dektronics/printalyzer-timer/enclosure/jigs/jig-power-board-2.stl

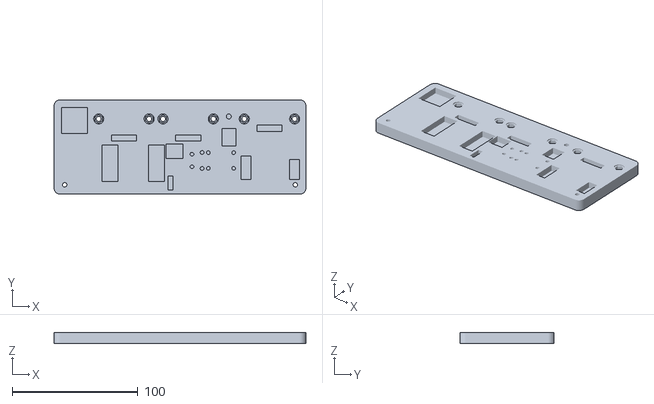
[picture p26: CAD file, 2024-06-14]
enclosure/jigs/jig-power-board-2.stl
200.0 x 75.0 x 9.00
