dektronics/printalyzer-timer/enclosure/meter-probe/meter-probe-bottom.3mf

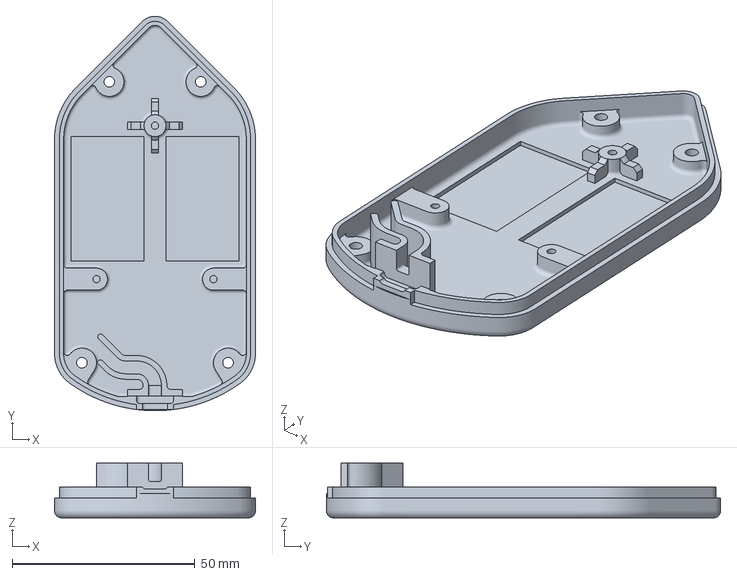
[picture p27: CAD file, 2026-03-26]
enclosure/meter-probe/meter-probe-bottom.3mf
55.0 x 107.9 x 15.0 mm
