dektronics/printalyzer-timer/enclosure/densistick/densistick-enclosure.step

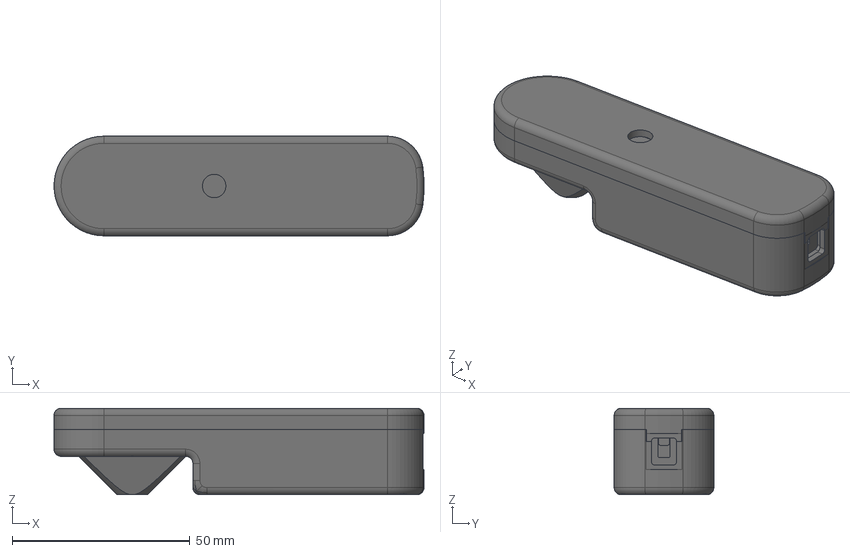
[picture p28: CAD file, 2026-03-26]
enclosure/densistick/densistick-enclosure.step
104.0 x 28.0 x 24.3 mm
Main Housing
Main Cover
Sensor Board Cover
Lower Filter Ring
Upper Filter Ring
