dektronics/printalyzer-timer/enclosure/meter-probe/meter-probe-top-rear.dxf

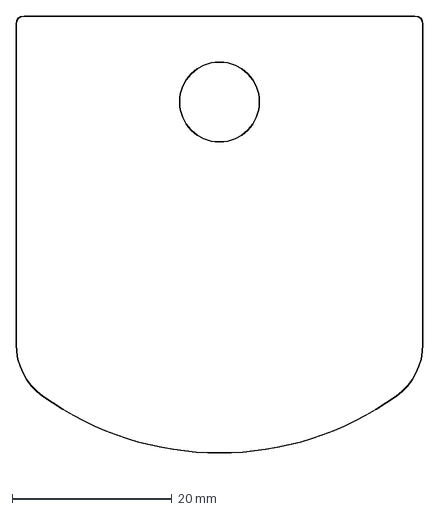
[picture p29: CAD file, 2024-02-04]
enclosure/meter-probe/meter-probe-top-rear.dxf
51.0 x 57.1 mm
