dektronics/printalyzer-timer/enclosure/base-unit/enclosure-base-flat.dxf

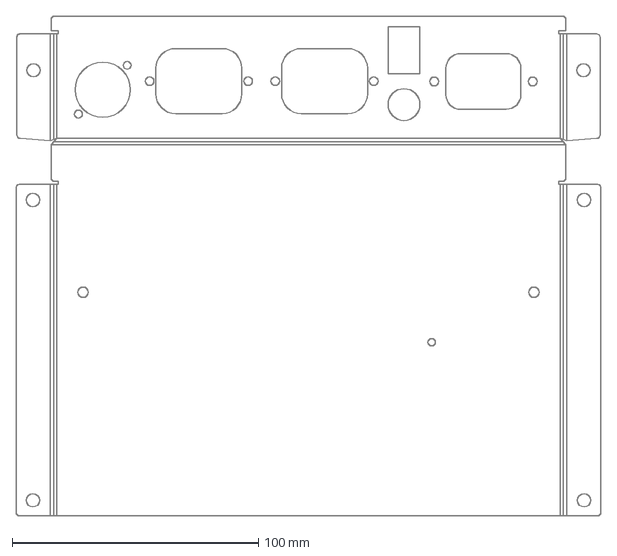
[picture p30: CAD file, 2026-03-26]
enclosure/base-unit/enclosure-base-flat.dxf
237.3 x 202.9 mm
