dektronics/printalyzer-timer/enclosure/densistick/densistick-cover.3mf

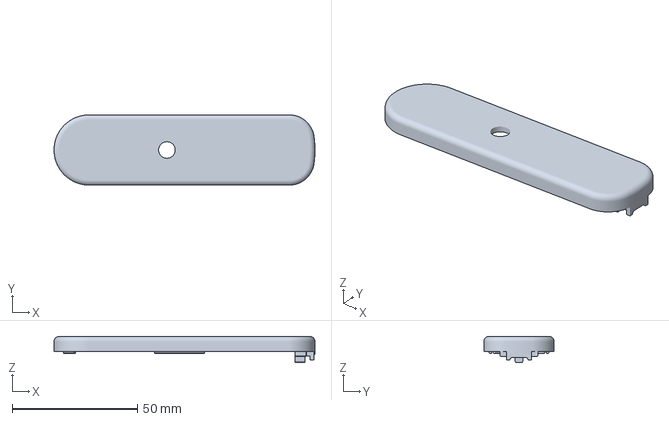
[picture p31: CAD file, 2026-03-26]
enclosure/densistick/densistick-cover.3mf
104.0 x 28.0 x 10.4 mm
