dektronics/printalyzer-timer/enclosure/meter-probe/meter-probe-top-front.dxf

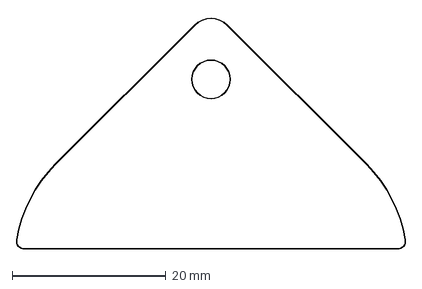
[picture p32: CAD file, 2024-02-04]
enclosure/meter-probe/meter-probe-top-front.dxf
50.6 x 30.3 mm
