dektronics/printalyzer-timer/enclosure/densistick/upper-filter-ring.dxf

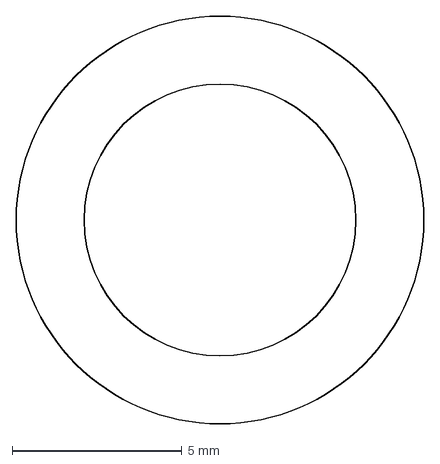
[picture p33: CAD file, 2024-08-25]
enclosure/densistick/upper-filter-ring.dxf
12.0 x 12.0 mm
