dektronics/printalyzer-timer/enclosure/densistick/densistick-overlay.dxf

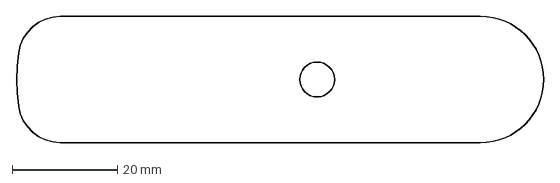
[picture p34: CAD file, 2024-08-25]
enclosure/densistick/densistick-overlay.dxf
100.1 x 24.0 mm
