dektronics/printalyzer-timer/enclosure/jigs/jig-power-board-1.stl

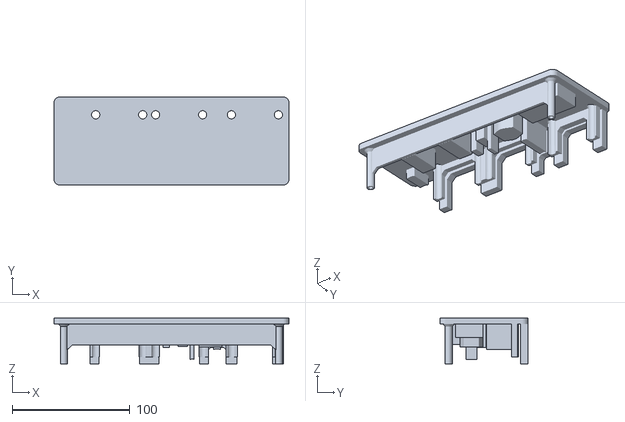
[picture p35: CAD file, 2024-06-14]
enclosure/jigs/jig-power-board-1.stl
200.0 x 75.0 x 39.0
