dektronics/printalyzer-timer/enclosure/meter-probe/meter-probe-top-rear-drawing.pdf

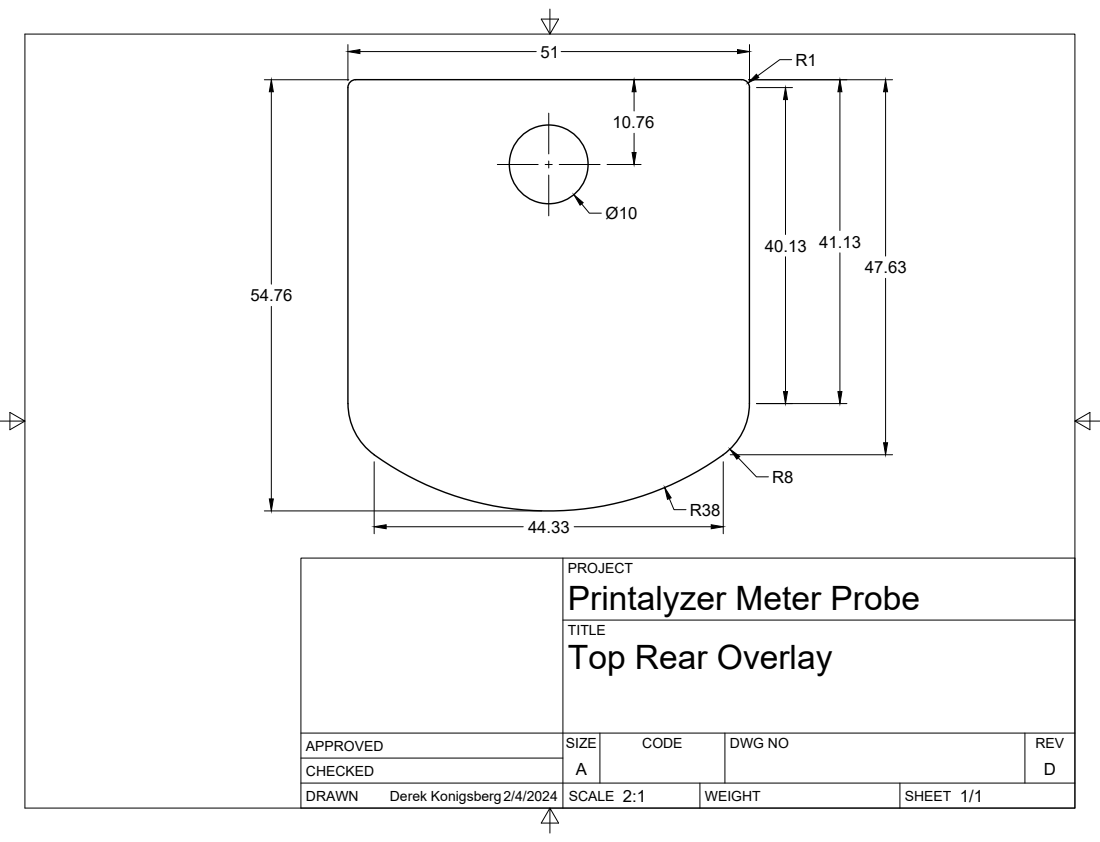
[picture p56: page 1]
SIZE; CODE; DWG NO; REV; Derek Konigsberg2/4/2024

PROJECT
Printalyzer Meter Probe
Top Rear Overlay
