dektronics/printalyzer-timer/enclosure/meter-probe/meter-probe-top-rear.pdf

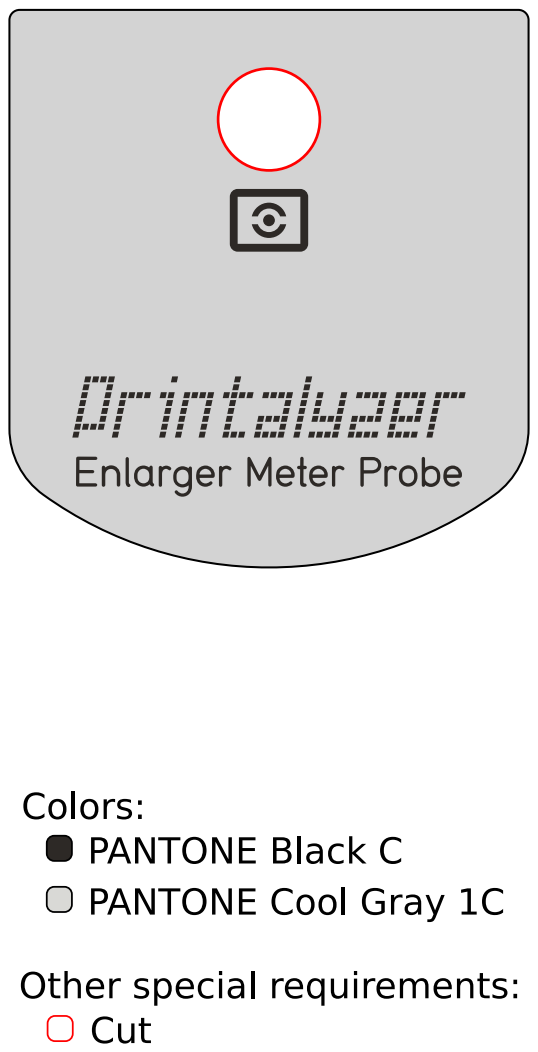
[picture p58: page 1]
