dektronics/printalyzer-timer/docs/cube/printalyzer-timer.ioc

Mcu.UserName=STM32F446RETx
PA0-WKUP.GPIO_Label=BUZZ_EN1 [Piezo]
PA0-WKUP.Signal=GPIO_Output
PA1.GPIO_Label=BUZZ_EN2 [Piezo]
PA1.Signal=GPIO_Output
PA10.Signal=USART1_RX
PA11.GPIO_Label=DMX512_RX_EN
PA11.Signal=GPIO_Output
PA13.Signal=SYS_JTMS-SWDIO
PA14.Signal=SYS_JTCK-SWCLK
PA15.Signal=SYS_JTDI
PA2.GPIO_Label=BUZZ_DIN [Piezo]
PA2.Signal=S_TIM9_CH1
PA4.GPIO_Label=DISP_CS [Display]
PA4.Signal=GPIO_Output
PA5.GPIO_Label=DISP_SCK [Display]
PA5.Signal=SPI1_SCK
PA6.GPIO_Label=DISP_DC [Display]
PA6.Signal=GPIO_Output
PA7.GPIO_Label=DISP_MOSI [Display]
PA7.Signal=SPI1_MOSI
PA8.GPIO_Label=ENC_CH1
PA8.Signal=S_TIM1_CH1
PA9.GPIO_Label=ENC_CH2
PA9.Signal=S_TIM1_CH2
PB0.GPIO_Label=LED_OE [LED Driver]
PB0.Signal=S_TIM3_CH3
PB10.Signal=I2C2_SCL
PB12.GPIO_Label=USB_HUB_RESET
PB12.Signal=GPIO_Output
PB13.GPIO_Label=USB_DRIVE_VBUS
PB13.Signal=GPIO_Output
PB14.Signal=USB_OTG_HS_DM
PB15.Signal=USB_OTG_HS_DP
PB3.Signal=SYS_JTDO-SWO
PB5.GPIO_Label=KEY_INT [Keypad]
PB5.Signal=GPXTI5
PB6.Signal=USART1_TX
PB7.Signal=I2C1_SDA
PB8.Signal=I2C1_SCL
PC1.GPIO_Label=LED_SDI [LED Driver]
PC1.Signal=SPI3_MOSI
PC10.GPIO_Label=LED_CLK [LED Driver]
PC10.Signal=SPI3_SCK
PC11.GPIO_Label=RELAY_SFLT [Safelight]
PC11.Signal=GPIO_Output
PC12.Signal=I2C2_SDA
PC2.GPIO_Label=LED_LE [LED Driver]
PC2.Signal=GPIO_Output
PC4.GPIO_Label=DISP_RESET [Display]
PC4.Signal=GPIO_Output
PC6.GPIO_Label=DMX512_TX
PC6.Signal=USART6_TX
PC7.GPIO_Label=DMX512_RX
PC7.Signal=USART6_RX
PC8.GPIO_Label=DMX512_TX_EN
PC8.Signal=GPIO_Output
PC9.GPIO_Label=USB_HUB_CLK
PC9.Signal=RCC_MCO_2
PD2.GPIO_Label=RELAY_ENLG [Enlarger]
PD2.Signal=GPIO_Output
PH0-OSC_IN.Signal=RCC_OSC_IN
PH1-OSC_OUT.Signal=RCC_OSC_OUT
