dektronics/printalyzer-timer/software/firmware/src/display/display_assets.c

#include "display_assets.h"

#include <string.h>

#define printalyzer_width 256
#define printalyzer_height 64
static const unsigned char printalyzer_bits[] = {
    0x00, 0x00, 0x00, 0x00, 0x00, 0x00, 0x00, 0x00, 0x00, 0x00, 0x00, 0x00,
    0x00, 0x00, 0x00, 0x00, 0x00, 0x00, 0x00, 0x00, 0x00, 0x00, 0x00, 0x00,
    0x00, 0x00, 0x00, 0x00, 0x00, 0x00, 0x00, 0x00, 0x00, 0x00, 0x00, 0x00,
    0x00, 0x00, 0x00, 0x00, 0x00, 0x00, 0x00, 0x00, 0x00, 0x00, 0x00, 0x00,
    0x00, 0x00, 0x00, 0x00, 0x00, 0x00, 0x00, 0x00, 0x00, 0x00, 0x00, 0x00,
    0x00, 0x00, 0x00, 0x00, 0x00, 0x00, 0x00, 0x00, 0x00, 0x00, 0x00, 0x00,
    0x00, 0x00, 0x00, 0x00, 0x00, 0x00, 0x00, 0x00, 0x00, 0x00, 0x00, 0x00,
    0x00, 0x00, 0x00, 0x00, 0x00, 0x00, 0x00, 0x00, 0x00, 0x00, 0x00, 0x00,
    0x00, 0x00, 0x00, 0x00, 0x00, 0x00, 0x00, 0x00, 0x00, 0x00, 0x00, 0x00,
    0x00, 0x00, 0x00, 0x00, 0x00, 0x00, 0x00, 0x00, 0x00, 0x00, 0x00, 0x00,
    0x00, 0x00, 0x00, 0x00, 0x00, 0x00, 0x00, 0x00, 0x00, 0x00, 0x00, 0x00,
    0x00, 0x00, 0x00, 0x00, 0x00, 0x00, 0x00, 0x00, 0x00, 0x00, 0x00, 0x00,
    0x00, 0x00, 0x00, 0x00, 0x00, 0x00, 0x00, 0x00, 0x00, 0x00, 0x00, 0x00,
    0x00, 0x00, 0x00, 0x00, 0x00, 0x00, 0x00, 0x00, 0x00, 0x00, 0x00, 0x00,
    0x00, 0x00, 0x00, 0x00, 0x00, 0x00, 0x00, 0x00, 0x00, 0x00, 0x00, 0x00,
    0x00, 0x00, 0x00, 0x00, 0x00, 0x00, 0x00, 0x00, 0x00, 0x00, 0x00, 0x00,
    0x00, 0x00, 0x00, 0x00, 0x00, 0x00, 0x00, 0x00, 0x00, 0x00, 0x00, 0x00,
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
    0x07, 0x63, 0x0c, 0x0e, 0x07, 0x07, 0x0e, 0x0e, 0x07, 0x0e, 0x07, 0x0e,
    0x07, 0xfc, 0x03, 0x0e, 0x07, 0xf0, 0x00, 0x0e, 0x07, 0x00, 0x00, 0x0e,
    0x07, 0x00, 0x00, 0x0e, 0xff, 0xff, 0xff, 0x0f, 0xfe, 0xff, 0xff, 0x07,
    0xf8, 0xff, 0xff, 0x01 };

#define dens_ind_refl_width 22
#define dens_ind_refl_height 22
static unsigned char dens_ind_refl_bits[] = {
    0x00, 0x0c, 0x00, 0x00, 0x0c, 0x00, 0x80, 0x7f, 0x00, 0xe0, 0xff, 0x01,
    0xf0, 0xcc, 0x03, 0x38, 0x0c, 0x07, 0x18, 0x00, 0x06, 0x1c, 0x00, 0x0e,
    0x0c, 0x00, 0x0c, 0x0c, 0x0c, 0x0c, 0x3f, 0x1e, 0x3f, 0x3f, 0x1e, 0x3f,
    0x0c, 0x0c, 0x0c, 0x0c, 0x00, 0x0c, 0x1c, 0x00, 0x0e, 0x18, 0x00, 0x06,
    0x38, 0x0c, 0x07, 0xf0, 0xcc, 0x03, 0xe0, 0xff, 0x01, 0x80, 0x7f, 0x00,
    0x00, 0x0c, 0x00, 0x00, 0x0c, 0x00 };

#define dens_ind_tran_width 22
#define dens_ind_tran_height 22
static unsigned char dens_ind_tran_bits[] = {
    0x00, 0x00, 0x00, 0x00, 0x0c, 0x00, 0x80, 0x7f, 0x00, 0xe0, 0xff, 0x01,
    0xf0, 0xc0, 0x03, 0x38, 0x00, 0x07, 0x18, 0x0c, 0x06, 0x1c, 0x0c, 0x0e,
    0x0c, 0x0c, 0x0c, 0x0c, 0x1e, 0x0c, 0xce, 0xff, 0x1c, 0xce, 0xff, 0x1c,
    0x0c, 0x1e, 0x0c, 0x0c, 0x0c, 0x0c, 0x1c, 0x0c, 0x0e, 0x18, 0x0c, 0x06,
    0x38, 0x00, 0x07, 0xf0, 0xc0, 0x03, 0xe0, 0xff, 0x01, 0x80, 0x7f, 0x00,
    0x00, 0x0c, 0x00, 0x00, 0x00, 0x00 };

#define ASSET_ENTRY(x) { x##_bits, x##_width, x##_height }

static const asset_info_t asset_list[] = {
    ASSET_ENTRY(printalyzer),
    ASSET_ENTRY(timer_icon_48),
    ASSET_ENTRY(timer_icon_32),
    ASSET_ENTRY(timer_icon_24),
    ASSET_ENTRY(timer_off_icon_24),
    ASSET_ENTRY(timer_off_icon_18),
    ASSET_ENTRY(exposure_adj_icon_48),
    ASSET_ENTRY(timer_adj_icon_48),
    ASSET_ENTRY(pev_adj_icon_48),
    ASSET_ENTRY(photo_icon_24),
    ASSET_ENTRY(adjust_icon_24),
    ASSET_ENTRY(adjust_count_1_18),
    ASSET_ENTRY(adjust_count_2_18),
    ASSET_ENTRY(adjust_count_3_18),
    ASSET_ENTRY(adjust_count_4_18),
    ASSET_ENTRY(adjust_count_5_18),
    ASSET_ENTRY(adjust_count_6_18),
    ASSET_ENTRY(adjust_count_7_18),
    ASSET_ENTRY(adjust_count_8_18),
    ASSET_ENTRY(adjust_count_9_18),
    ASSET_ENTRY(adjust_count_9p_18),
    ASSET_ENTRY(arrow_up_18),
    ASSET_ENTRY(arrow_down_18),
    ASSET_ENTRY(adjust_count_1_32),
    ASSET_ENTRY(adjust_count_2_32),
    ASSET_ENTRY(adjust_count_3_32),
    ASSET_ENTRY(adjust_count_4_32),
    ASSET_ENTRY(adjust_count_5_32),
    ASSET_ENTRY(adjust_count_6_32),
    ASSET_ENTRY(adjust_count_7_32),
    ASSET_ENTRY(adjust_count_8_32),
    ASSET_ENTRY(adjust_count_9_32),
    ASSET_ENTRY(adjust_count_9p_32),
    ASSET_ENTRY(paper_index_1_18),
    ASSET_ENTRY(paper_index_2_18),
    ASSET_ENTRY(paper_index_3_18),
    ASSET_ENTRY(paper_index_4_18),
    ASSET_ENTRY(paper_index_5_18),
    ASSET_ENTRY(paper_index_6_18),
    ASSET_ENTRY(paper_index_7_18),
    ASSET_ENTRY(paper_index_8_18),
    ASSET_ENTRY(paper_index_9_18),
    ASSET_ENTRY(paper_index_10_18),
    ASSET_ENTRY(paper_index_11_18),
    ASSET_ENTRY(paper_index_12_18),
    ASSET_ENTRY(paper_index_13_18),
    ASSET_ENTRY(paper_index_14_18),
    ASSET_ENTRY(paper_index_15_18),
    ASSET_ENTRY(paper_index_16_18),
    ASSET_ENTRY(dens_ind_probe),
    ASSET_ENTRY(dens_ind_refl),
    ASSET_ENTRY(dens_ind_tran)
};

uint8_t display_asset_get(asset_info_t *asset_info, asset_name_t asset_name)
{
    if (asset_info && asset_name >= 0 && asset_name < ASSET_MAX) {
        memcpy(asset_info, &asset_list[asset_name], sizeof(asset_info_t));
        return 1;
    } else {
        return 0;
    }
}
