dektronics/printalyzer-timer/software/firmware/src/menu/menu_import_export.c

#include "menu_import_export.h"

#include <stdio.h>
#include <string.h>
#include <stdlib.h>
#include <stdbool.h>
#include <math.h>
#include <errno.h>
#include <ctype.h>
#include <ff.h>

#define LOG_TAG "menu_import_export"
#include <elog.h>
#include <illum_controller.h>

#include "display.h"
#include "settings.h"
#include "usb_host.h"
#include "core_json.h"
#include "util.h"
#include "json_util.h"
#include "file_picker.h"
#include "app_descriptor.h"

/*
 * Fixed filename for configuration import/export.
 * Once a file browser is available, this should simply become the
 * default choice for export.
 */
#define CONF_FILENAME "printalyzer-conf.dat"

/*
 * Maximum allowed size of the configuration file, since the entire file
 * is loaded into memory for parsing. If anything bigger is required, then
 * the parser needs to be redesigned to be able to work incrementally
 * off the file.
 */
#define MAX_CONF_FILE_SIZE 32768

#define HEADER_EXPORT_VERSION     1
#define CONFIG_EXPORT_VERSION     1
#define SAFELIGHT_EXPORT_VERSION  1
#define ENLARGER_EXPORT_VERSION   1
#define PAPER_EXPORT_VERSION      1
#define STEP_WEDGE_EXPORT_VERSION 1

typedef struct {
    bool has_valid_header;
    bool has_settings;
    bool has_safelight;
    int has_enlargers;
    int has_papers;
    bool has_step_wedge;
} conf_file_properties_t;

static menu_result_t menu_import_config(state_controller_t *controller);
static bool import_config_file(const char *filename, bool *reload_paper);
static bool parse_file_properties(conf_file_properties_t *file_properties, const char *buf, UINT len);
static bool validate_section_header(const char *buf, size_t len);
static menu_result_t import_section_prompt(conf_file_properties_t *file_properties);
static int parse_section_version(const char *buf, size_t len);
static bool import_section_settings(const char *buf, size_t len, int *enlarger_config_index, int *paper_profile_index);
static bool import_section_safelight(const char *buf, size_t len);
static int import_section_enlargers(const char *buf, size_t len);
static bool parse_section_enlarger(const char *buf, size_t len, enlarger_config_t *config);
static void parse_section_enlarger_control(const char *buf, size_t len, enlarger_control_t *control);
static void parse_section_enlarger_control_grade_values(const char *buf, size_t len, enlarger_control_t *control);
static void parse_section_enlarger_control_grade_entry(const char *buf, size_t len, enlarger_grade_values_t *grade_values);
static void parse_section_enlarger_timing(const char *buf, size_t len, enlarger_timing_t *timing);
static int import_section_papers(const char *buf, size_t len);
static bool parse_section_paper(const char *buf, size_t len, paper_profile_t *profile);
static void parse_section_paper_grades(const char *buf, size_t len, paper_profile_t *profile);
static void parse_section_paper_grade_entry(const char *buf, size_t len, paper_profile_grade_t *grade);
static bool import_section_step_wedge(const char *buf, size_t len);

static menu_result_t menu_export_config();
static bool export_config_file(const char *filename);
static bool write_section_header(FIL *fp);
static bool write_section_config(FIL *fp);
static bool write_section_safelight(FIL *fp);
static bool write_section_enlargers(FIL *fp);
static bool write_section_papers(FIL *fp);
static bool write_section_step_wedge(FIL *fp);

menu_result_t menu_import_export(state_controller_t *controller)
{
    log_i("Import/Export menu");

    menu_result_t menu_result = MENU_OK;
    uint8_t option = 1;

    do {
        option = display_selection_list(
                "Import / Export Configuration", option,
                "Import from USB device\n"
                "Export to USB device");

        if (option == 1) {
            menu_result = menu_import_config(controller);
        } else if (option == 2) {
            menu_result = menu_export_config();
        } else if (option == UINT8_MAX) {
            menu_result = MENU_TIMEOUT;
        }
    } while (option > 0 && menu_result != MENU_TIMEOUT);

    return menu_result;
}

menu_result_t menu_import_config(state_controller_t *controller)
{
    char buf[256];
    char path_buf[256];
    uint8_t option;
    bool reload_paper = false;

    if (!usb_msc_is_mounted()) {
        option = display_message(
                "Import from USB device",
                NULL,
                "\n"
                "Please insert a USB storage\n"
                "device and try again.\n", " OK ");
        if (option == UINT8_MAX) {
            return MENU_TIMEOUT;
        } else {
            return MENU_OK;
        }
    }

    option = file_picker_show("Select Configuration File", path_buf, sizeof(path_buf), NULL);
    if (option == MENU_TIMEOUT) {
        return MENU_TIMEOUT;
    } else if (option != MENU_OK) {
        return MENU_OK;
    }

    if (import_config_file(path_buf, &reload_paper)) {
        char filename[33];
        if (file_picker_expand_filename(filename, 33, path_buf)) {
            filename[32] = '\0';
        } else {
            sprintf(filename, "----");
        }
        sprintf(buf,
            "\n"
            "Configuration loaded from file:\n"
            "%s\n", filename);
        option = display_message(
            "Import from USB device",
            NULL, buf, " OK ");
    } else {
        option = display_message(
            "Import from USB device",
            NULL,
            "\n"
            "Configuration was not loaded\n", " OK ");
    }

    /* Reload active profiles that may have changed */
    state_controller_reload_enlarger_config(controller);
    if (reload_paper) {
        state_controller_reload_paper_profile(controller, true);
    }

    illum_controller_refresh();

    if (option == UINT8_MAX) {
        return MENU_TIMEOUT;
    } else {
        return MENU_OK;
    }
}

bool import_config_file(const char *filename, bool *reload_paper)
{
    FRESULT res;
    FIL fp;
    bool file_open = false;
    bool success = false;
    char *file_buf = NULL;
    UINT bytes_read = 0;
    JSONStatus_t status;
    size_t start = 0;
    size_t next = 0;
    JSONPair_t pair = {0};
    conf_file_properties_t file_properties = {0};
    int enlarger_config_index = -1;
    int paper_profile_index = -1;
    int imported_enlargers = -1;
    int imported_papers = -1;
    menu_result_t menu_result;

    do {
        memset(&fp, 0, sizeof(FIL));

        res = f_open(&fp, filename, FA_READ | FA_OPEN_EXISTING);
        if (res != FR_OK) {
            log_e("Error opening config file: %d", res);
            break;
        }
        file_open = true;

        if (f_size(&fp) > MAX_CONF_FILE_SIZE) {
            log_e("File is too large: %lu > %d", f_size(&fp), MAX_CONF_FILE_SIZE);
            break;
        }

        log_i("Config file opened: %s", filename);

        /* Allocate buffer for file */
        file_buf = pvPortMalloc(f_size(&fp));
        if (!file_buf) {
            log_e("Unable to allocate buffer for file: %lu", f_size(&fp));
            break;
        }

        /* Read file into buffer */
        if (f_read(&fp, file_buf, f_size(&fp), &bytes_read) != FR_OK) {
            log_e("Error reading file");
            break;
        }
        if (bytes_read != f_size(&fp)) {
            log_e("Short read: %d != %lu", bytes_read, f_size(&fp));
            break;
        }

        /* Close file */
        f_close(&fp);
        file_open = false;

        log_i("Config file loaded into buffer");

        /* Validate the JSON */
        if (JSON_Validate(file_buf, bytes_read) != JSONSuccess) {
            log_w("JSON invalid");
            break;
        }

        log_i("Config file validated as JSON");

        /* Traverse the top level to see what sections are in the file */
        if (!parse_file_properties(&file_properties, file_buf, bytes_read)) {
            display_message(
                "Import from USB device",
                NULL,
                "\n"
                "File does not contain any\n"
                "configurations.\n", " OK ");
            break;
        }

        /* Show user prompt of sections to import */
        menu_result = import_section_prompt(&file_properties);
        if (menu_result != MENU_SAVE) {
            /* No sections were selected */
            break;
        }

        log_i("Selected sections: settings=%d, safelight=%d, enlargers=%d, papers=%d, step_wedge=%d",
            file_properties.has_settings, file_properties.has_safelight,
            file_properties.has_enlargers, file_properties.has_papers,
            file_properties.has_step_wedge);

        /* Traverse the top level and import any selected sections */
        start = 0;
        next = 0;
        status = JSON_Iterate(file_buf, bytes_read, &start, &next, &pair);
        while (status == JSONSuccess) {
            if (!pair.key) { continue; }

            if (strncmp("settings", pair.key, pair.keyLength) == 0 && pair.jsonType == JSONObject) {
                if (file_properties.has_settings) {
                    import_section_settings(pair.value, pair.valueLength, &enlarger_config_index, &paper_profile_index);
                }
            } else if (strncmp("safelight", pair.key, pair.keyLength) == 0 && pair.jsonType == JSONObject) {
                if (file_properties.has_safelight) {
                    import_section_safelight(pair.value, pair.valueLength);
                }
            } else if (strncmp("enlargers", pair.key, pair.keyLength) == 0 && pair.jsonType == JSONArray) {
                if (file_properties.has_enlargers) {
                    imported_enlargers = import_section_enlargers(pair.value, pair.valueLength);
                }
            } else if (strncmp("papers", pair.key, pair.keyLength) == 0 && pair.jsonType == JSONArray) {
                if (file_properties.has_papers) {
                    imported_papers = import_section_papers(pair.value, pair.valueLength);
                }
            } else if (strncmp("step_wedge", pair.key, pair.keyLength) == 0 && pair.jsonType == JSONObject) {
                if (file_properties.has_step_wedge) {
                    import_section_step_wedge(pair.value, pair.valueLength);
                }
            }

            status = JSON_Iterate(file_buf, bytes_read, &start, &next, &pair);
        }

        success = true;
    } while (0);

    /* Set default indices for enlarger and paper sections */
    if (file_properties.has_enlargers && imported_enlargers > 0 && enlarger_config_index >= 0) {
        if (enlarger_config_index < imported_enlargers) {
            settings_set_default_enlarger_config_index(enlarger_config_index);
        } else {
            settings_set_default_enlarger_config_index(0);
        }
    }
    if (file_properties.has_papers && imported_papers > 0 && paper_profile_index >= 0) {
        if (paper_profile_index < imported_papers) {
            settings_set_default_paper_profile_index(paper_profile_index);
        } else {
            settings_set_default_paper_profile_index(0);
        }
        if (reload_paper) { *reload_paper = true; }
    }

    if (file_open) {
        f_close(&fp);
    }
    if (file_buf) {
        vPortFree(file_buf);
    }

    return success;
}

bool parse_file_properties(conf_file_properties_t *file_properties, const char *buf, UINT len)
{
    size_t start = 0;
    size_t next = 0;
    JSONPair_t pair = {0};
    JSONStatus_t status;

    memset(file_properties, 0, sizeof(conf_file_properties_t));

    status = JSON_Iterate(buf, len, &start, &next, &pair);
    while (status == JSONSuccess) {
        if (pair.key) {
            if (strncmp("header", pair.key, pair.keyLength) == 0 && pair.jsonType == JSONObject) {
                file_properties->has_valid_header = validate_section_header(pair.value, pair.valueLength);
                if (!file_properties->has_valid_header) {
                    break;
                }
            } else if (strncmp("settings", pair.key, pair.keyLength) == 0 && pair.jsonType == JSONObject) {
                file_properties->has_settings = json_count_elements(pair.value, pair.valueLength) > 0;
            } else if (strncmp("safelight", pair.key, pair.keyLength) == 0 && pair.jsonType == JSONObject) {
                file_properties->has_safelight = json_count_elements(pair.value, pair.valueLength) > 0;
            } else if (strncmp("enlargers", pair.key, pair.keyLength) == 0 && pair.jsonType == JSONArray) {
                file_properties->has_enlargers = json_count_elements(pair.value, pair.valueLength);
            } else if (strncmp("papers", pair.key, pair.keyLength) == 0 && pair.jsonType == JSONArray) {
                file_properties->has_papers = json_count_elements(pair.value, pair.valueLength);
            } else if (strncmp("step_wedge", pair.key, pair.keyLength) == 0 && pair.jsonType == JSONObject) {
                file_properties->has_step_wedge = json_count_elements(pair.value, pair.valueLength) > 0;
            }
        }

        status = JSON_Iterate(buf, len, &start, &next, &pair);
    }

    if (!file_properties->has_valid_header) {
        log_w("File does not contain valid header");
        return false;
    }
    log_i("Found valid header");

    log_i("Found sections: settings=%d, safelight=%d, enlargers=%d, papers=%d, step_wedge=%d",
        file_properties->has_settings, file_properties->has_safelight,
        file_properties->has_enlargers, file_properties->has_papers,
        file_properties->has_step_wedge);

    if (!file_properties->has_settings && !file_properties->has_safelight
        && file_properties->has_enlargers == 0 && file_properties->has_papers == 0
        && !file_properties->has_step_wedge) {
        log_w("File has no sections");
        return false;
    }

    return true;
}

bool validate_section_header(const char *buf, size_t len)
{
    JSONStatus_t status;
    size_t start = 0;
    size_t next = 0;
    JSONPair_t pair = {0};
    int version = -1;
    bool has_device = false;

    status = JSON_Iterate(buf, len, &start, &next, &pair);
    while (status == JSONSuccess) {
        if (!pair.key) { continue; }

        if (strncmp("version", pair.key, pair.keyLength) == 0 && pair.jsonType == JSONNumber) {
            version = json_parse_int(pair.value, pair.valueLength, 0);
        } else if (strncmp("device", pair.key, pair.keyLength) == 0 && pair.jsonType == JSONString) {
            has_device = (strncasecmp(pair.value, "Printalyzer", pair.valueLength) == 0);
        }

        status = JSON_Iterate(buf, len, &start, &next, &pair);
    }

    return (version == HEADER_EXPORT_VERSION && has_device);
}

menu_result_t import_section_prompt(conf_file_properties_t *file_properties)
{
    char buf[256];
    size_t offset = 0;
    uint8_t option = 0;
    uint8_t index = 0;
    menu_result_t menu_result = MENU_OK;
    bool select_settings = true;
    bool select_safelight = true;
    bool select_enlargers = true;
    bool select_papers = true;
    bool select_step_wedge = true;
    uint8_t index_settings = 0;
    uint8_t index_safelight = 0;
    uint8_t index_enlargers = 0;
    uint8_t index_papers = 0;
    uint8_t index_step_wedge = 0;
    uint8_t index_import = 0;

    do {
        index = 0;
        offset = 0;
        if (file_properties->has_settings) {
            offset += sprintf(buf + offset, select_settings ? "[*]" : "[ ]");
            offset += sprintf(buf + offset, " Settings                    \n");
            index_settings = ++index;
        }
        if (file_properties->has_safelight) {
            offset += sprintf(buf + offset, select_safelight ? "[*]" : "[ ]");
            offset += sprintf(buf + offset, " Safelight configuration     \n");
            index_safelight = ++index;
        }
        if (file_properties->has_enlargers > 0) {
            offset += sprintf(buf + offset, select_enlargers ? "[*]" : "[ ]");
            sprintf(buf + offset, " Enlarger profiles (%d)", file_properties->has_enlargers);
            offset += pad_str_to_length(buf + offset, ' ', DISPLAY_MENU_ROW_LENGTH - 3);
            offset += sprintf(buf + offset, "\n");
            index_enlargers = ++index;
        }
        if (file_properties->has_papers > 0) {
            offset += sprintf(buf + offset, select_papers ? "[*]" : "[ ]");
            sprintf(buf + offset, " Paper profiles (%d)", file_properties->has_papers);
            offset += pad_str_to_length(buf + offset, ' ', DISPLAY_MENU_ROW_LENGTH - 3);
            offset += sprintf(buf + offset, "\n");
            index_papers = ++index;
        }
        if (file_properties->has_step_wedge) {
            offset += sprintf(buf + offset, select_step_wedge ? "[*]" : "[ ]");
            offset += sprintf(buf + offset, " Step wedge properties       \n");
            index_step_wedge = ++index;
        }
        sprintf(buf + offset, "*** Import selected ***");
        index_import = ++index;

        option = display_selection_list("Import from USB device", option, buf);
        if (option == index_settings) {
            select_settings = !select_settings;
        } else if (option == index_safelight) {
            select_safelight = !select_safelight;
        } else if (option == index_enlargers) {
            select_enlargers = !select_enlargers;
        } else if (option == index_papers) {
            select_papers = !select_papers;
        } else if (option == index_step_wedge) {
            select_step_wedge = !select_step_wedge;
        } else if (option == index_import) {
            if (!select_settings && !select_safelight
                && !select_enlargers && !select_papers
                && !select_step_wedge) {
                continue;
            }
            if (index_settings > 0) {
                file_properties->has_settings = select_settings;
            }
            if (index_safelight > 0) {
                file_properties->has_safelight = select_safelight;
            }
            if (index_enlargers > 0) {
                file_properties->has_enlargers = select_enlargers ? file_properties->has_enlargers : 0;
            }
            if (index_papers > 0) {
                file_properties->has_papers = select_papers ? file_properties->has_papers : 0;
            }
            if (index_step_wedge) {
                file_properties->has_step_wedge = select_step_wedge;
            }
            menu_result = MENU_SAVE;
            break;
        } else if (option == UINT8_MAX) {
            menu_result = MENU_TIMEOUT;
            break;
        }
    } while (option > 0);

    return menu_result;
}

int parse_section_version(const char *buf, size_t len)
{
    JSONStatus_t status;
    size_t start = 0;
    size_t next = 0;
    JSONPair_t pair = {0};
    int version = -1;

    status = JSON_Iterate(buf, len, &start, &next, &pair);
    while (status == JSONSuccess) {
        if (pair.key) {
            if (strncmp("version", pair.key, pair.keyLength) == 0 && pair.jsonType == JSONNumber) {
                version = json_parse_int(pair.value, pair.valueLength, 0);
                break;
            }
        }
        status = JSON_Iterate(buf, len, &start, &next, &pair);
    }

    return version;
}
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
